paulbuzzby/e-inkCalendar/helpers.py

from email.mime import image
from string import Formatter
from datetime import timedelta
from PIL import Image

#https://stackoverflow.com/questions/538666/format-timedelta-to-string
def strfdelta(tdelta, fmt='{D:02}d {H:02}h {M:02}m {S:02}s', inputtype='timedelta'):
    """Convert a datetime.timedelta object or a regular number to a custom-
    formatted string, just like the stftime() method does for datetime.datetime
    objects.

    The fmt argument allows custom formatting to be specified.  Fields can 
    include seconds, minutes, hours, days, and weeks.  Each field is optional.

    Some examples:
        '{D:02}d {H:02}h {M:02}m {S:02}s' --> '05d 08h 04m 02s' (default)
        '{W}w {D}d {H}:{M:02}:{S:02}'     --> '4w 5d 8:04:02'
        '{D:2}d {H:2}:{M:02}:{S:02}'      --> ' 5d  8:04:02'
        '{H}h {S}s'                       --> '72h 800s'

    The inputtype argument allows tdelta to be a regular number instead of the  
    default, which is a datetime.timedelta object.  Valid inputtype strings: 
        's', 'seconds', 
        'm', 'minutes', 
        'h', 'hours', 
        'd', 'days', 
        'w', 'weeks'
    """

    # Convert tdelta to integer seconds.
    if inputtype == 'timedelta':
        remainder = int(tdelta.total_seconds())
    elif inputtype in ['s', 'seconds']:
        remainder = int(tdelta)
    elif inputtype in ['m', 'minutes']:
        remainder = int(tdelta)*60
    elif inputtype in ['h', 'hours']:
        remainder = int(tdelta)*3600
    elif inputtype in ['d', 'days']:
        remainder = int(tdelta)*86400
    elif inputtype in ['w', 'weeks']:
        remainder = int(tdelta)*604800

    f = Formatter()
    desired_fields = [field_tuple[1] for field_tuple in f.parse(fmt)]
    possible_fields = ('W', 'D', 'H', 'M', 'S')
    constants = {'W': 604800, 'D': 86400, 'H': 3600, 'M': 60, 'S': 1}
    values = {}
    for field in possible_fields:
        if field in desired_fields and field in constants:
            values[field], remainder = divmod(remainder, constants[field])
    return f.format(fmt, **values)

#https://stackoverflow.com/questions/30227466/combine-several-images-horizontally-with-python
def append_images(images, direction='horizontal',
                  bg_color=(255,255,255), aligment='center') -> image:
    """
    Appends images in horizontal/vertical direction.

    Args:
        images: List of PIL images
        direction: direction of concatenation, 'horizontal' or 'vertical'
        bg_color: Background color (default: white)
        aligment: alignment mode if images need padding;
           'left', 'right', 'top', 'bottom', or 'center'

    Returns:
        Concatenated image as a new PIL image object.
    """
    widths, heights = zip(*(i.size for i in images))

    if direction=='horizontal':
        new_width = sum(widths)
        new_height = max(heights)
    else:
        new_width = max(widths)
        new_height = sum(heights)

    new_im = Image.new('RGB', (new_width, new_height), color=bg_color)


    offset = 0
    for im in images:
        if direction=='horizontal':
            y = 0
            if aligment == 'center':
                y = int((new_height - im.size[1])/2)
            elif aligment == 'bottom':
                y = new_height - im.size[1]
            new_im.paste(im, (offset, y))
            offset += im.size[0]
        else:
            x = 0
            if aligment == 'center':
                x = int((new_width - im.size[0])/2)
            elif aligment == 'right':
                x = new_width - im.size[0]
            new_im.paste(im, (x, offset))
            offset += im.size[1]

    return new_im
